xfbs/audio-mixer/images/175-16-QSOP.jpg

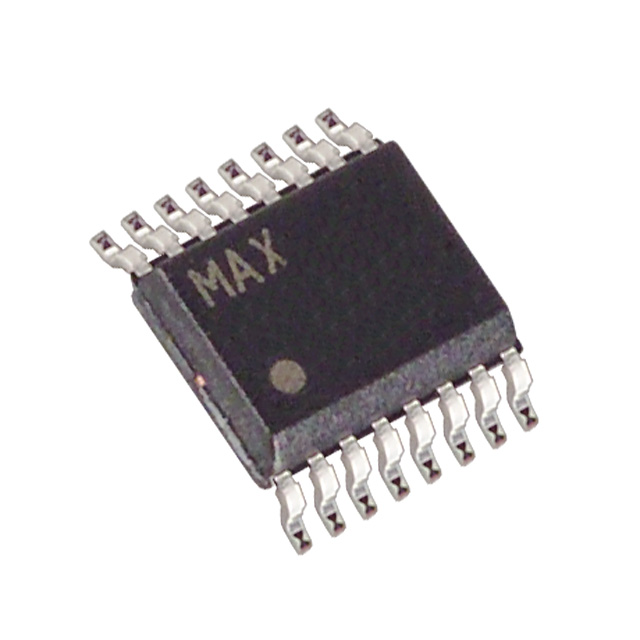
images/175-16-QSOP.jpg
