xfbs/audio-mixer/images/MFG_PJ-037A.jpg

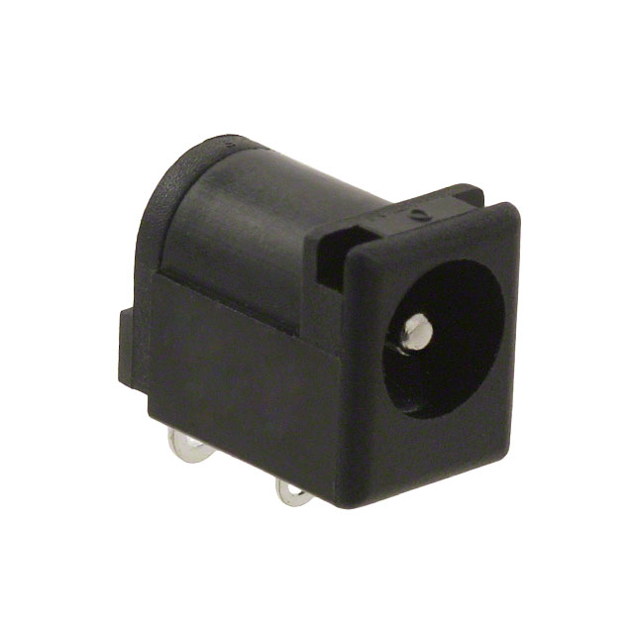
images/MFG_PJ-037A.jpg
