xfbs/audio-mixer/images/nichion47cap.jpg

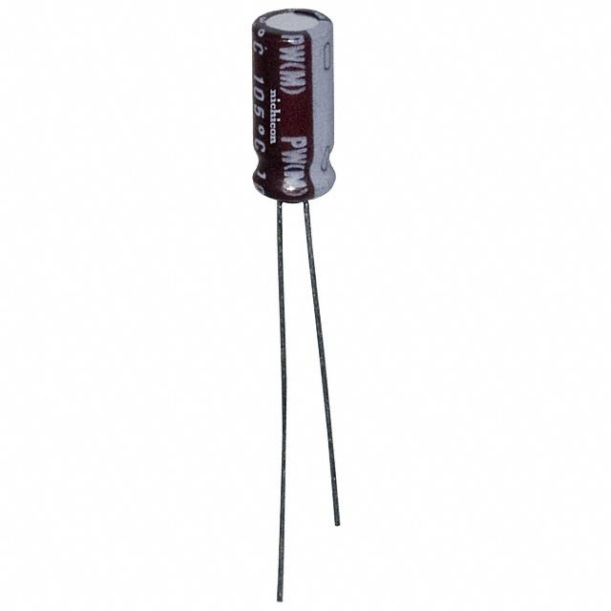
images/nichion47cap.jpg
