xfbs/audio-mixer/images/soic6.jpg

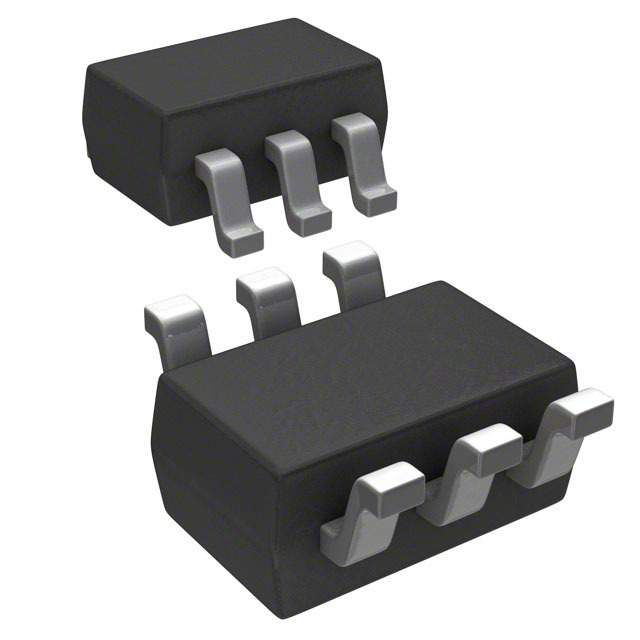
images/soic6.jpg
